PUT-Motorsport/PUTM_EV_LAPTIMER/firmware/main/drivers/include/wifi_driver.h

#pragma once

#include "defines.h"

#include "esp_wifi.h"

#ifdef __cplusplus
extern "C"
{
#endif

    esp_err_t wifi_init();
    esp_err_t wifi_start(wifi_mode_t wifi_mode, char wifi_ssid[WIFI_SSID_STR_LENGTH], char wifi_password[WIFI_PASSWORD_STR_LENGTH]);
    esp_err_t wifi_restart(wifi_mode_t wifi_mode, char wifi_ssid[WIFI_SSID_STR_LENGTH], char wifi_password[WIFI_PASSWORD_STR_LENGTH]);
    esp_err_t wifi_get_ip(char ip_string[WIFI_IP_LENGTH]);
    esp_err_t wifi_get_mode(wifi_mode_t *wifi_mode);

#ifdef __cplusplus
}
#endif
