PUT-Motorsport/PUTM_EV_LAPTIMER/firmware/config.txt

{
    "two_gate_mode" : 0,
    "wifi_config" : {
        "mode" : 0,
        "ssid" : "PUTM_LAPTIMER",
        "password" : ""
    },
    "driver_list" : ["aaa", "bbb", "ccc"]
}
