PUT-Motorsport/PUTM_EV_LAPTIMER/firmware/main/drivers/lcd.c

#include "lcd.h"

#include "lvgl.h"
#include "esp_lvgl_port.h"
#include "esp_lcd_ili9341.h"

#include "driver/spi_master.h"

static const char *TAG = "LCD";

esp_err_t lcd_init(void)
{
    ESP_LOGI(TAG, "Initialize SPI bus");
    spi_bus_config_t buscfg = {
        .sclk_io_num = CONFIG_LCD_SPI_CLK,
        .mosi_io_num = CONFIG_LCD_SPI_MOSI,
        .miso_io_num = -1,
        .quadwp_io_num = -1,
        .quadhd_io_num = -1,
        .max_transfer_sz = 0,
    };
    ESP_ERROR_CHECK(spi_bus_initialize(SPI3_HOST, &buscfg, SPI_DMA_CH_AUTO));

    ESP_LOGI(TAG, "Install panel IO");
    esp_lcd_panel_io_handle_t io_handle = NULL;
    esp_lcd_panel_io_spi_config_t io_config = {
        .dc_gpio_num = CONFIG_LCD_DC,
        .cs_gpio_num = CONFIG_LCD_SPI_CS,
        .pclk_hz = 10 * 1000 * 1000,
        .lcd_cmd_bits = 8,
        .lcd_param_bits = 8,
        .spi_mode = 0,
        .trans_queue_depth = 10,
    };

    ESP_ERROR_CHECK(esp_lcd_new_panel_io_spi(SPI3_HOST, &io_config, &io_handle));

    esp_lcd_panel_handle_t panel_handle = NULL;
    esp_lcd_panel_dev_config_t panel_config = {
        .reset_gpio_num = -1,
        .rgb_ele_order = LCD_RGB_ELEMENT_ORDER_BGR,
        .bits_per_pixel = 16,
    };

    ESP_LOGI(TAG, "Install ILI9431 panel driver");
    ESP_ERROR_CHECK(esp_lcd_new_panel_ili9341(io_handle, &panel_config, &panel_handle));
    ESP_ERROR_CHECK(esp_lcd_panel_reset(panel_handle));
    ESP_ERROR_CHECK(esp_lcd_panel_init(panel_handle));
    ESP_ERROR_CHECK(esp_lcd_panel_mirror(panel_handle, true, false));
    ESP_ERROR_CHECK(esp_lcd_panel_disp_on_off(panel_handle, true));

    ESP_LOGI(TAG, "Initialize LVGL");
    lvgl_port_cfg_t lvgl_cfg = ESP_LVGL_PORT_INIT_CONFIG();
    lvgl_cfg.task_affinity = 1;
    lvgl_cfg.task_stack_caps = MALLOC_CAP_SPIRAM;

    ESP_ERROR_CHECK(lvgl_port_init(&lvgl_cfg));

    const lvgl_port_display_cfg_t disp_cfg = {
        .io_handle = io_handle,
        .panel_handle = panel_handle,
        .buffer_size = LCD_RES_H * LCD_RES_V,
        .trans_size = LCD_RES_H * LCD_RES_V,
        .double_buffer = true,
        .hres = LCD_RES_H,
        .vres = LCD_RES_V,
        .monochrome = false,
        .color_format = LV_COLOR_FORMAT_RGB565,
        .rotation = {
            .swap_xy = true,
            .mirror_x = false,
            .mirror_y = false,
        },
        .flags = {
            .buff_spiram = true,
            .buff_dma = true,
            .swap_bytes = true,
            .sw_rotate = false,
        }};
    lvgl_port_add_disp(&disp_cfg);
    return ESP_OK;
}
